antmicro/jetson-agx-thor-baseboard-enclosure/step/raised-cheese-head-screw-din-7985-m4-x-8-h-steel-4-6-plain-v1.step

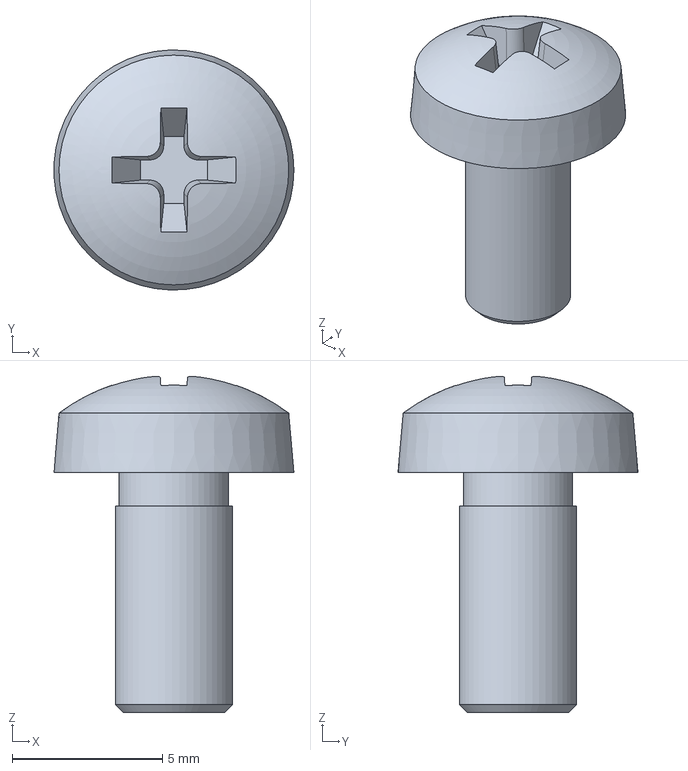
[picture p17: CAD file, 2026-04-10]
step/raised-cheese-head-screw-din-7985-m4-x-8-h-steel-4-6-plain-v1.step
7.99 x 8.00 x 11.2 mm
